Fra4prg/KitchenTimer/src/Kitchen_Timer/Alarm_Clock.h

// Audacity sample rate 8000Hz, export WAV "other uncompressed files" / Unsigned 8-bit PCM
// xxd -i "Alarm Clock_cut.wav" Alarm_Clock.h

unsigned char PROGMEM Alarm_Clock[28614] = {
  0x52, 0x49, 0x46, 0x46, 0xbe, 0x6f, 0x00, 0x00, 0x57, 0x41, 0x56, 0x45,
  0x66, 0x6d, 0x74, 0x20, 0x28, 0x00, 0x00, 0x00, 0xfe, 0xff, 0x01, 0x00,
  0x40, 0x1f, 0x00, 0x00, 0x40, 0x1f, 0x00, 0x00, 0x01, 0x00, 0x08, 0x00,
  0x16, 0x00, 0x08, 0x00, 0x04, 0x00, 0x00, 0x00, 0x01, 0x00, 0x00, 0x00,
  0x00, 0x00, 0x10, 0x00, 0x80, 0x00, 0x00, 0xaa, 0x00, 0x38, 0x9b, 0x71,
  0x66, 0x61, 0x63, 0x74, 0x04, 0x00, 0x00, 0x00, 0x76, 0x6f, 0x00, 0x00,
  0x64, 0x61, 0x74, 0x61, 0x76, 0x6f, 0x00, 0x00, 0xc1, 0x75, 0x4a, 0x9a,
  0xaa, 0x67, 0x3c, 0xde, 0x5a, 0x55, 0xb7, 0xa2, 0x37, 0x4d, 0xff, 0x42,
  0x53, 0xbe, 0x7e, 0x44, 0x79, 0xdf, 0x3a, 0x8b, 0x8f, 0x70, 0x7f, 0x64,
  0xd4, 0x5c, 0x45, 0x87, 0xe5, 0x42, 0x15, 0xff, 0x51, 0x0c, 0xf0, 0xbb,
  0x00, 0x9d, 0xff, 0x00, 0xa6, 0xff, 0x05, 0x20, 0xfd, 0x9c, 0x10, 0xec,
  0x64, 0x39, 0xb5, 0x6c, 0x7b, 0xae, 0x85, 0x23, 0xce, 0x6d, 0x48, 0xff,
  0x26, 0x10, 0xff, 0xae, 0x00, 0xe0, 0xff, 0x00, 0xae, 0xff, 0x00, 0x2e,
  0xff, 0x2c, 0x00, 0xff, 0x83, 0x00, 0xc5, 0xc1, 0x35, 0xc9, 0xb8, 0x00,
  0x95, 0x7b, 0x25, 0xff, 0xbf, 0x00, 0x8b, 0xac, 0x1f, 0xff, 0xd6, 0x00,
  0x87, 0xff, 0x00, 0x66, 0xfb, 0x0e, 0x67, 0xff, 0x10, 0x00, 0xff, 0xf0,
  0x47, 0x64, 0x79, 0x4f, 0xa9, 0xdc, 0x48, 0x4f, 0xa3, 0x54, 0x86, 0xc2,
  0x63, 0x80, 0xa8, 0x1c, 0x82, 0xff, 0x20, 0x5f, 0xf0, 0x30, 0x54, 0xe8,
  0x53, 0x48, 0xe1, 0x65, 0x4c, 0xb8, 0x65, 0x70, 0x96, 0x78, 0x97, 0x82,
  0x59, 0x91, 0x87, 0x68, 0xb6, 0x6f, 0x5f, 0xa7, 0x55, 0x7a, 0xba, 0x66,
  0x7d, 0x9b, 0x50, 0x8a, 0x9f, 0x5f, 0xa3, 0x8f, 0x4a, 0x94, 0x86, 0x5e,
  0xb2, 0x87, 0x52, 0xa1, 0x73, 0x5f, 0xae, 0x7c, 0x70, 0xa2, 0x63, 0x6b,
  0xa5, 0x69, 0x89, 0xa9, 0x52, 0x7c, 0x9d, 0x58, 0x92, 0xa9, 0x5d, 0x8a,
  0x83, 0x5a, 0x9c, 0x91, 0x68, 0xa0, 0x79, 0x50, 0xa2, 0x83, 0x6f, 0xac,
  0x75, 0x5d, 0x9b, 0x70, 0x77, 0xa8, 0x70, 0x7c, 0x92, 0x55, 0x85, 0xa2,
  0x65, 0x8b, 0x97, 0x51, 0x81, 0xa7, 0x72, 0x74, 0x7c, 0x92, 0x93, 0x54,
  0x6f, 0xcb, 0x5d, 0x4a, 0xe0, 0x7d, 0x23, 0xb4, 0xab, 0x34, 0x93, 0xa4,
  0x50, 0x94, 0x89, 0x62, 0xac, 0x77, 0x72, 0x9b, 0x4d, 0x89, 0xbe, 0x47,
  0x80, 0xba, 0x41, 0x7f, 0xa6, 0x57, 0x92, 0xa0, 0x4f, 0x99, 0x93, 0x4b,
  0xae, 0x8f, 0x40, 0xaa, 0x9a, 0x3d, 0x9a, 0xa4, 0x63, 0x8b, 0x7e, 0x6b,
  0x98, 0x79, 0x76, 0xa3, 0x70, 0x68, 0x99, 0x69, 0x7f, 0xaf, 0x6c, 0x6d,
  0x9a, 0x73, 0x72, 0x96, 0x79, 0x89, 0x84, 0x65, 0x8e, 0x85, 0x6e, 0x9d,
  0x82, 0x62, 0x98, 0x75, 0x6b, 0xaf, 0x70, 0x64, 0xa9, 0x73, 0x61, 0xa0,
  0x7a, 0x7c, 0x9b, 0x63, 0x7c, 0x8f, 0x62, 0x95, 0xaa, 0x57, 0x86, 0x95,
  0x58, 0x94, 0x96, 0x5d, 0x93, 0x8e, 0x53, 0x9c, 0x91, 0x6a, 0x98, 0x74,
  0x65, 0x9e, 0x70, 0x73, 0xb4, 0x68, 0x66, 0xa7, 0x62, 0x6e, 0xb6, 0x69,
  0x75, 0xa5, 0x5b, 0x7b, 0xa3, 0x66, 0x88, 0x99, 0x57, 0x89, 0x92, 0x62,
  0xa3, 0x8d, 0x54, 0x9b, 0x80, 0x59, 0xab, 0x86, 0x62, 0xa4, 0x71, 0x5d,
  0xa6, 0x79, 0x74, 0xa6, 0x64, 0x6d, 0xa2, 0x65, 0x81, 0xa5, 0x60, 0x82,
  0x92, 0x5a, 0x92, 0x98, 0x62, 0x9a, 0x87, 0x4f, 0x9e, 0x8a, 0x60, 0xa8,
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
};
unsigned int Alarm_Clock_cut_wav_len = 28614;
