Fra4prg/KitchenTimer/src/Kitchen_Timer/DSEG7_Classic_Mini_Bold_72.h

// Created by http://oleddisplay.squix.ch/ Consider a donation
// In case of problems make sure that you are using the font file with the correct version!
const uint8_t DSEG7_Classic_Mini_Bold_72Bitmaps[] PROGMEM = {

	// Bitmap Data:
	0x00, // ' '
	0x00, // '!'
	0xFF,0xFF,0xEF,0xFF,0xFE,0xC0,0x00,0x6C,0x00,0x06,0xC0,0x00,0x6C,0x00,0x06,0xC0,0x00,0x6C,0x00,0x06,0xC0,0x00,0x6C,0x00,0x06,0xC0,0x00,0x6C,0x00,0x06,0xC0,0x00,0x6C,0x00,0x06,0xC0,0x00,0x6C,0x00,0x06,0xC0,0x00,0x6C,0x00,0x06,0xC0,0x00,0x6C,0x00,0x06,0xC0,0x00,0x6C,0x00,0x06,0xC0,0x00,0x6C,0x00,0x06,0xC0,0x00,0x6C,0x00,0x06,0xC0,0x00,0x6C,0x00,0x06,0xC0,0x00,0x6C,0x00,0x06,0xC0,0x00,0x6C,0x00,0x06,0xC0,0x00,0x6C,0x00,0x06,0xC0,0x00,0x6C,0x00,0x06,0xC0,0x00,0x6C,0x00,0x06,0xC0,0x00,0x6C,0x00,0x06,0xC0,0x00,0x6C,0x00,0x06,0xC0,0x00,0x6C,0x00,0x06,0xC0,0x00,0x6C,0x00,0x06,0xFF,0xFF,0xEF,0xFF,0xFE, // '"'
	0xFF,0xFF,0xEF,0xFF,0xFE,0xC0,0x00,0x6C,0x00,0x06,0xC0,0x00,0x6C,0x00,0x06,0xC0,0x00,0x6C,0x00,0x06,0xC0,0x00,0x6C,0x00,0x06,0xC0,0x00,0x6C,0x00,0x06,0xC0,0x00,0x6C,0x00,0x06,0xC0,0x00,0x6C,0x00,0x06,0xC0,0x00,0x6C,0x00,0x06,0xC0,0x00,0x6C,0x00,0x06,0xC0,0x00,0x6C,0x00,0x06,0xC0,0x00,0x6C,0x00,0x06,0xC0,0x00,0x6C,0x00,0x06,0xC0,0x00,0x6C,0x00,0x06,0xC0,0x00,0x6C,0x00,0x06,0xC0,0x00,0x6C,0x00,0x06,0xC0,0x00,0x6C,0x00,0x06,0xC0,0x00,0x6C,0x00,0x06,0xC0,0x00,0x6C,0x00,0x06,0xC0,0x00,0x6C,0x00,0x06,0xC0,0x00,0x6C,0x00,0x06,0xC0,0x00,0x6C,0x00,0x06,0xC0,0x00,0x6C,0x00,0x06,0xFF,0xFF,0xEF,0xFF,0xFE, // '#'
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
	  {  7638,  40,  67,  60,    7,  -72 }, // 'F'
	  {  7973,  46,  72,  60,    7,  -72 }, // 'G'
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
};
const GFXfont DSEG7_Classic_Mini_Bold_72 PROGMEM = {
(uint8_t  *)DSEG7_Classic_Mini_Bold_72Bitmaps,(GFXglyph *)DSEG7_Classic_Mini_Bold_72Glyphs,0x20, 0x7E, 79};
