Fra4prg/KitchenTimer/src/Kitchen_Timer/harp.h

// Audacity sample rate 8000Hz, export WAV "other uncompressed files" / Unsigned 8-bit PCM
// xxd -i "Alarm Clock_cut.wav" Alarm_Clock.h

unsigned char PROGMEM harp[7732] = {
  0x52, 0x49, 0x46, 0x46, 0x2c, 0x1e, 0x00, 0x00, 0x57, 0x41, 0x56, 0x45,
  0x66, 0x6d, 0x74, 0x20, 0x28, 0x00, 0x00, 0x00, 0xfe, 0xff, 0x01, 0x00,
  0x40, 0x1f, 0x00, 0x00, 0x40, 0x1f, 0x00, 0x00, 0x01, 0x00, 0x08, 0x00,
  0x16, 0x00, 0x08, 0x00, 0x04, 0x00, 0x00, 0x00, 0x01, 0x00, 0x00, 0x00,
  0x00, 0x00, 0x10, 0x00, 0x80, 0x00, 0x00, 0xaa, 0x00, 0x38, 0x9b, 0x71,
  0x66, 0x61, 0x63, 0x74, 0x04, 0x00, 0x00, 0x00, 0xe3, 0x1d, 0x00, 0x00,
  0x64, 0x61, 0x74, 0x61, 0xe3, 0x1d, 0x00, 0x00, 0x7f, 0x7f, 0x80, 0x7f,
  0x80, 0x7f, 0x80, 0x7f, 0x82, 0x85, 0x84, 0x85, 0x84, 0x84, 0x84, 0x84,
  0x84, 0x84, 0x84, 0x84, 0x84, 0x84, 0x84, 0x84, 0x84, 0x84, 0x84, 0x84,
  0x84, 0x84, 0x84, 0x84, 0x84, 0x84, 0x84, 0x84, 0x84, 0x84, 0x84, 0x84,
  0x84, 0x84, 0x84, 0x84, 0x84, 0x84, 0x84, 0x84, 0x84, 0x84, 0x84, 0x84,
  0x84, 0x84, 0x84, 0x84, 0x84, 0x85, 0x85, 0x85, 0x85, 0x85, 0x85, 0x85,
  0x84, 0x84, 0x84, 0x85, 0x84, 0x84, 0x84, 0x84, 0x84, 0x84, 0x84, 0x84,
  0x85, 0x85, 0x85, 0x85, 0x84, 0x85, 0x85, 0x85, 0x85, 0x84, 0x84, 0x84,
  0x84, 0x84, 0x84, 0x84, 0x84, 0x84, 0x84, 0x84, 0x84, 0x84, 0x84, 0x84,
  0x85, 0x85, 0x85, 0x85, 0x85, 0x85, 0x85, 0x85, 0x85, 0x84, 0x84, 0x84,
  0x84, 0x84, 0x84, 0x84, 0x84, 0x84, 0x84, 0x85, 0x84, 0x84, 0x84, 0x85,
  0x85, 0x85, 0x85, 0x85, 0x85, 0x85, 0x85, 0x85, 0x84, 0x84, 0x84, 0x84,
  0x84, 0x84, 0x84, 0x84, 0x84, 0x84, 0x84, 0x83, 0x83, 0x84, 0x83, 0x84,
  0x84, 0x84, 0x84, 0x84, 0x85, 0x85, 0x86, 0x85, 0x84, 0x84, 0x85, 0x85,
  0x85, 0x86, 0x85, 0x85, 0x84, 0x83, 0x83, 0x83, 0x83, 0x83, 0x83, 0x83,
  0x84, 0x84, 0x84, 0x84, 0x84, 0x85, 0x85, 0x85, 0x85, 0x85, 0x85, 0x85,
  0x84, 0x84, 0x83, 0x83, 0x83, 0x83, 0x84, 0x84, 0x83, 0x83, 0x83, 0x83,
  0x84, 0x84, 0x83, 0x83, 0x84, 0x84, 0x84, 0x84, 0x84, 0x84, 0x85, 0x87,
  0x88, 0x86, 0x85, 0x86, 0x86, 0x86, 0x82, 0x86, 0x84, 0x84, 0x88, 0x86,
  0x83, 0x81, 0x85, 0x83, 0x7d, 0x7b, 0x85, 0x84, 0x7f, 0x7e, 0x7f, 0x89,
  0x8c, 0x89, 0x86, 0x87, 0x88, 0x8a, 0x82, 0x77, 0x7b, 0x82, 0x82, 0x7b,
  0x83, 0x86, 0x84, 0x89, 0x88, 0x85, 0x82, 0x84, 0x86, 0x86, 0x82, 0x8e,
  0x95, 0x8e, 0x90, 0x8b, 0x8a, 0x8a, 0x87, 0x80, 0x7d, 0x7d, 0x7e, 0x7d,
  0x77, 0x74, 0x77, 0x7c, 0x79, 0x7b, 0x81, 0x7f, 0x83, 0x87, 0x88, 0x87,
  0x89, 0x8c, 0x8d, 0x8a, 0x8b, 0x95, 0x90, 0x90, 0x8f, 0x8b, 0x8a, 0x88,
  0x84, 0x7f, 0x7e, 0x7b, 0x7e, 0x7f, 0x7a, 0x75, 0x78, 0x7b, 0x78, 0x7c,
  0x7f, 0x7f, 0x83, 0x87, 0x85, 0x85, 0x88, 0x8a, 0x8b, 0x88, 0x90, 0x92,
  0x8e, 0x91, 0x8f, 0x8b, 0x8a, 0x89, 0x82, 0x83, 0x80, 0x7e, 0x81, 0x81,
  0x7d, 0x77, 0x7d, 0x7a, 0x78, 0x7c, 0x7c, 0x7b, 0x80, 0x84, 0x80, 0x85,
  0x85, 0x8a, 0x89, 0x87, 0x90, 0x91, 0x90, 0x8f, 0x8d, 0x8a, 0x8d, 0x89,
  0x86, 0x85, 0x81, 0x83, 0x84, 0x82, 0x79, 0x7a, 0x7c, 0x77, 0x78, 0x7b,
  0x7a, 0x7c, 0x83, 0x80, 0x83, 0x84, 0x85, 0x89, 0x84, 0x88, 0x8d, 0x90,
  0x90, 0x90, 0x8c, 0x8e, 0x8e, 0x89, 0x8a, 0x84, 0x81, 0x83, 0x85, 0x7f,
  0x7a, 0x7d, 0x79, 0x78, 0x7b, 0x7c, 0x79, 0x80, 0x82, 0x80, 0x83, 0x80,
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
};
unsigned int harp_wav_len = 7732;
